infrared5/massroute-pi/Art/Models/Textures/Picture_Texture.png

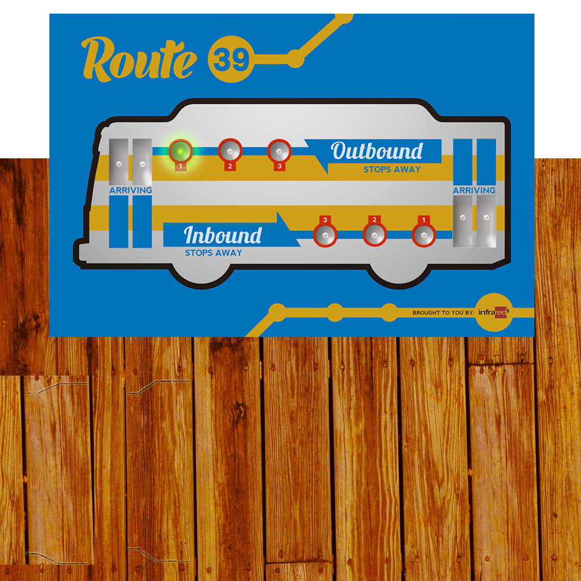
Art/Models/Textures/Picture_Texture.png
