infrared5/massroute-pi/Art/Models/Textures/PictureUV.png

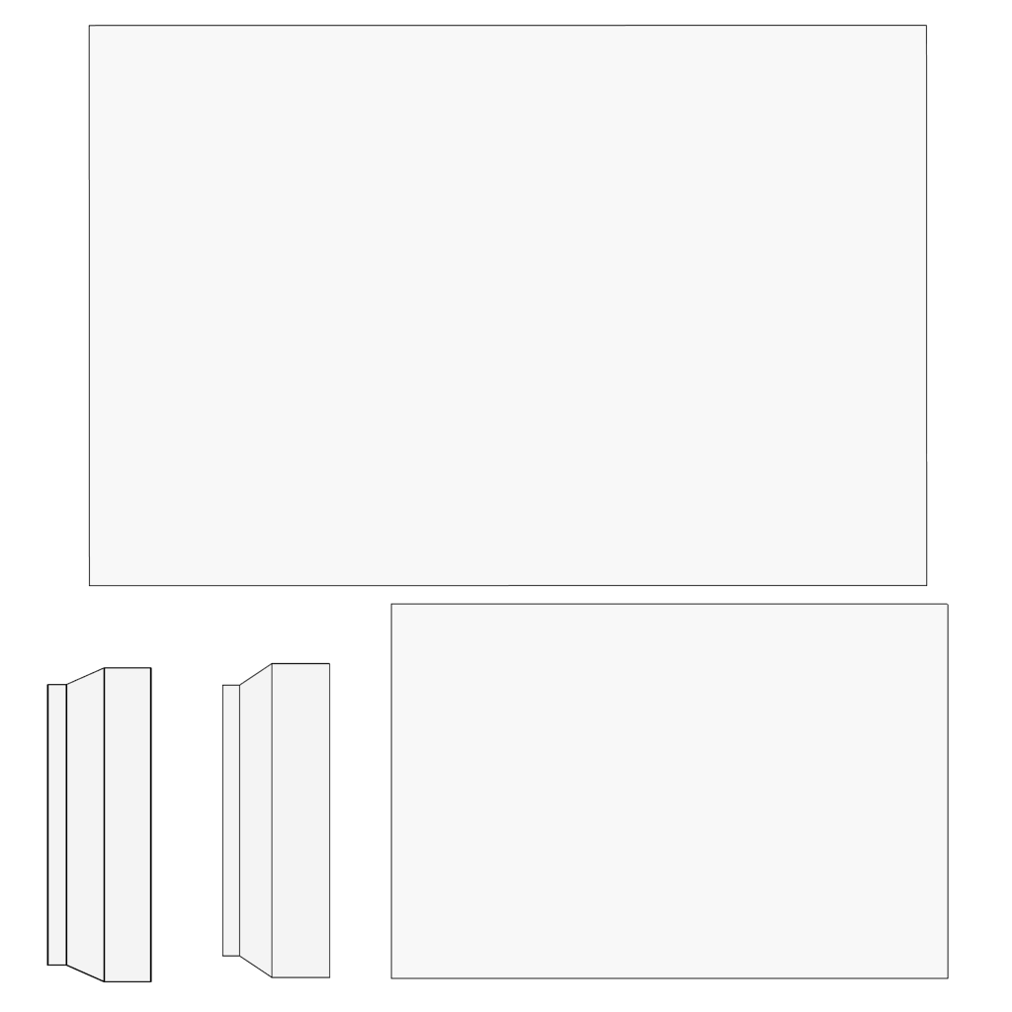
Art/Models/Textures/PictureUV.png
