infrared5/massroute-pi/Art/Research/Americana/4-500x344.jpg

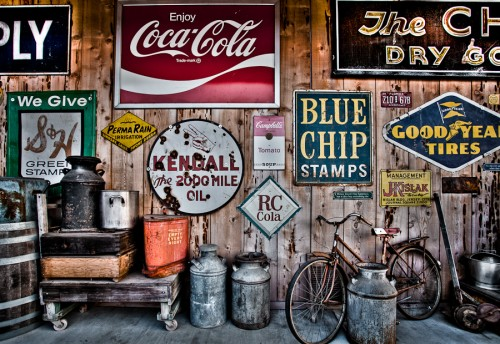
Art/Research/Americana/4-500x344.jpg
