infrared5/massroute-pi/Art/Research/Americana/2363436134_2fb481de5b.jpg

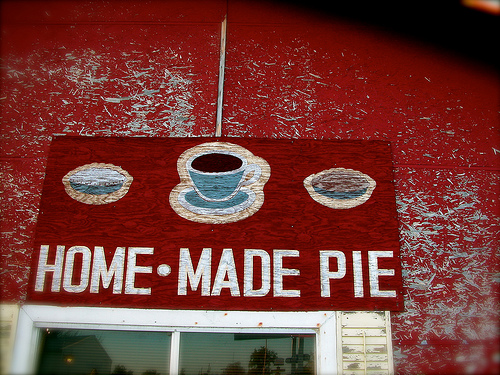
Art/Research/Americana/2363436134_2fb481de5b.jpg
