infrared5/massroute-pi/Art/Research/Americana/200773309354_1_0_1.jpg

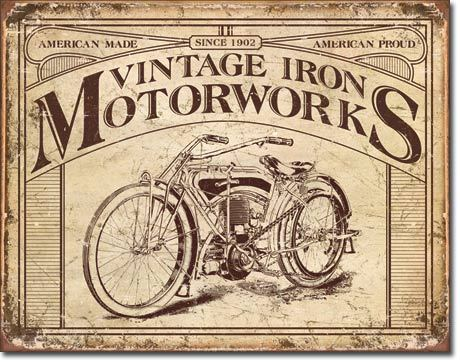
Art/Research/Americana/200773309354_1_0_1.jpg
