infrared5/massroute-pi/Art/Research/Americana/$(KGrHqZHJBME63Uw4Y8SBO76!MFf,g~~60_35.JPG

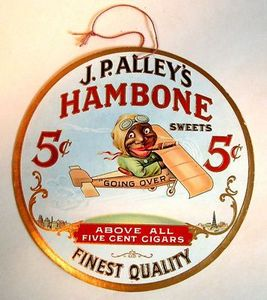
Art/Research/Americana/$(KGrHqZHJBME63Uw4Y8SBO76!MFf,g~~60_35.JPG
