infrared5/massroute-pi/Art/Research/Americana/dont-be-a-drip.jpg

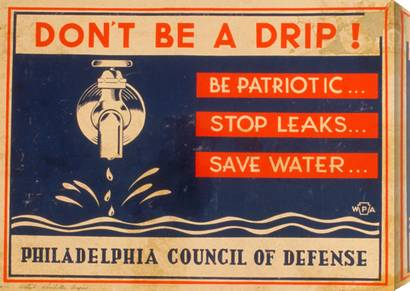
Art/Research/Americana/dont-be-a-drip.jpg
