infrared5/massroute-pi/Art/Research/Americana/il_fullxfull.299568161.jpg

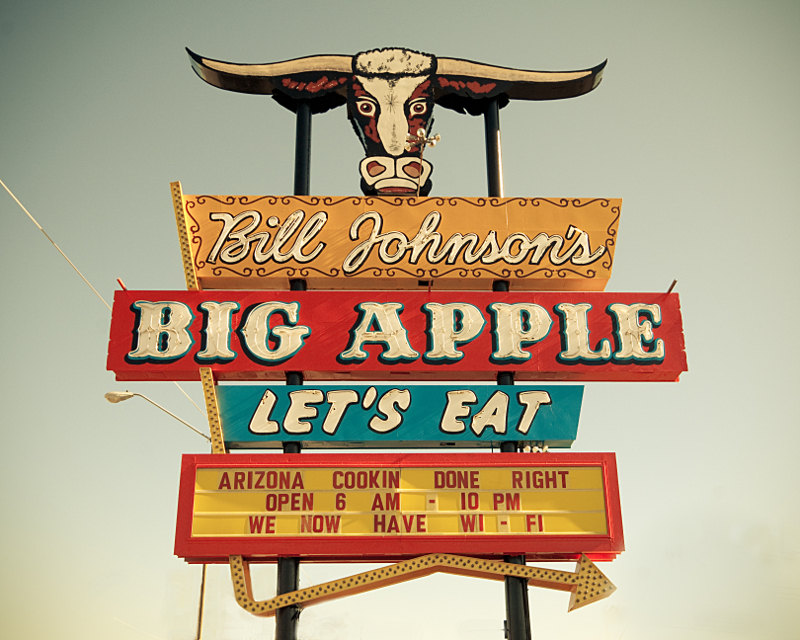
Art/Research/Americana/il_fullxfull.299568161.jpg
