infrared5/massroute-pi/Art/Research/Americana/mX-IDmk9UM7dmhiOSRjjnaw.jpg

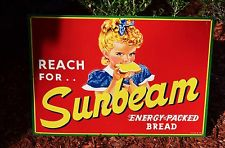
Art/Research/Americana/mX-IDmk9UM7dmhiOSRjjnaw.jpg
