infrared5/massroute-pi/Art/Research/Americana/redhorsesigns_se.jpg

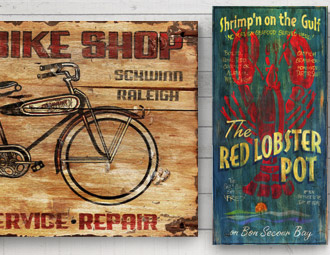
Art/Research/Americana/redhorsesigns_se.jpg
