infrared5/massroute-pi/Art/Research/Americana/set_of_2_vintage_look_advertising_wooden_signs.jpg

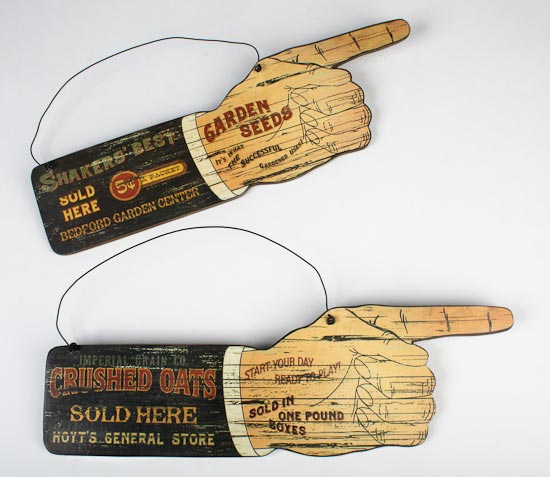
Art/Research/Americana/set_of_2_vintage_look_advertising_wooden_signs.jpg
