infrared5/massroute-pi/Art/Research/Americana/SummerTyne-copy.jpg

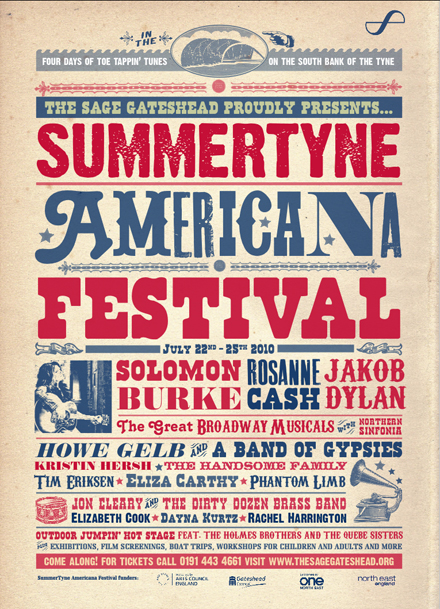
Art/Research/Americana/SummerTyne-copy.jpg
