infrared5/massroute-pi/Art/Research/Bauhaus/bauhaus4.jpg

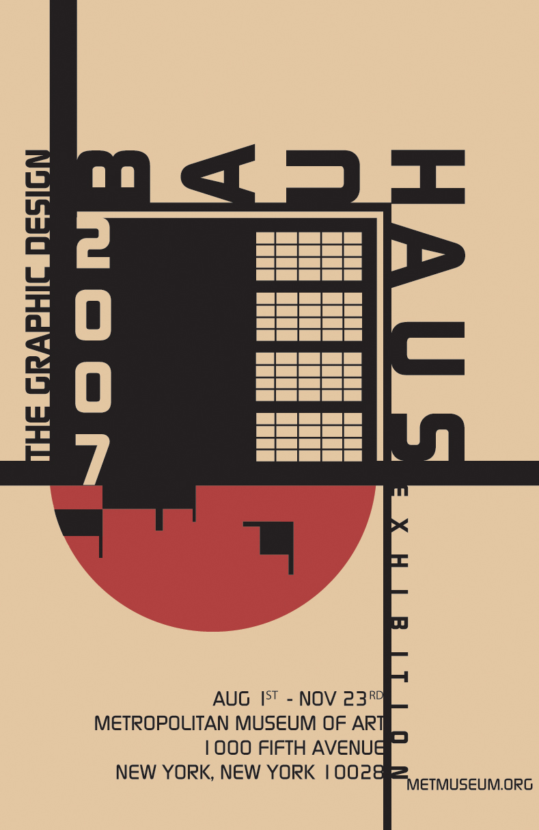
Art/Research/Bauhaus/bauhaus4.jpg
