infrared5/massroute-pi/Art/Research/Bauhaus/bauhaus.jpg

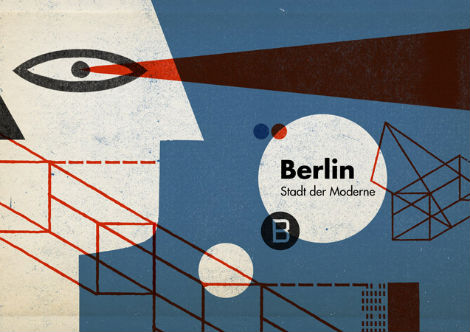
Art/Research/Bauhaus/bauhaus.jpg
