infrared5/massroute-pi/Art/Research/Bauhaus/bauhaus_11.jpg

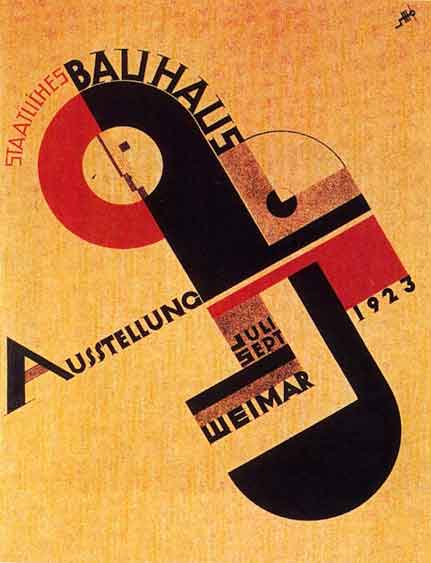
Art/Research/Bauhaus/bauhaus_11.jpg
