infrared5/massroute-pi/Art/Research/Bauhaus/Bauhaus_lecture.jpg

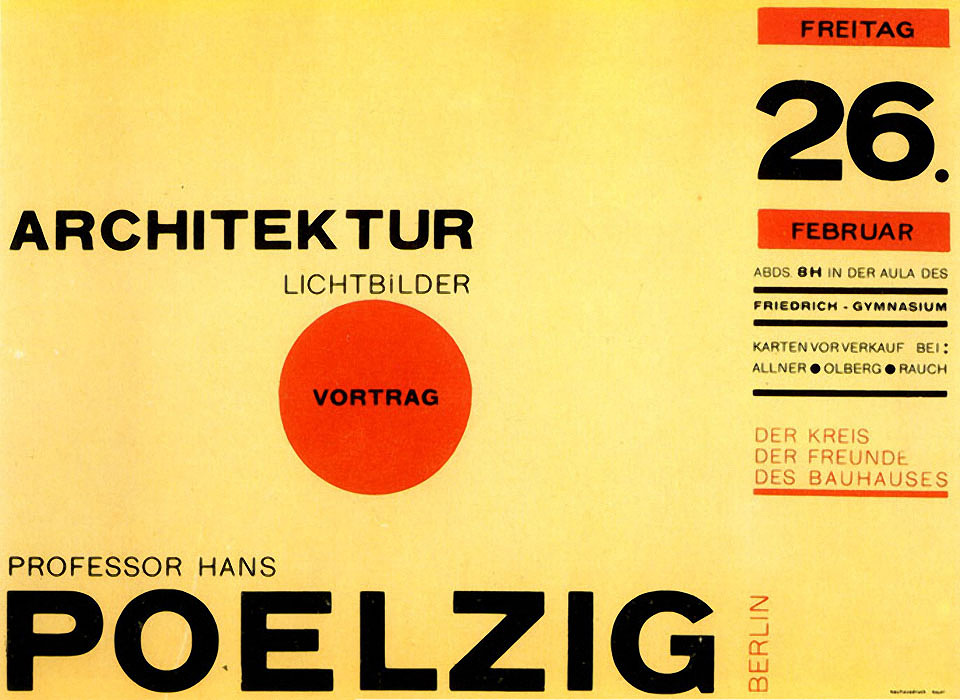
Art/Research/Bauhaus/Bauhaus_lecture.jpg
