infrared5/massroute-pi/Art/Research/Bauhaus/Factory-A-by-Josef-Albers-001.jpg

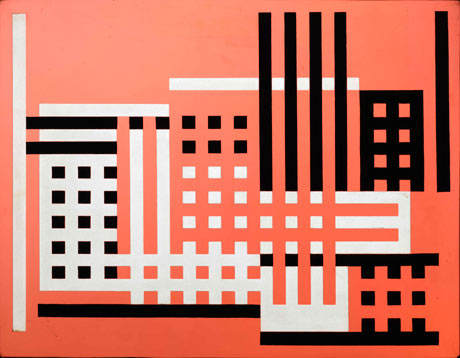
Art/Research/Bauhaus/Factory-A-by-Josef-Albers-001.jpg
