infrared5/massroute-pi/Art/Research/Bauhaus/original_299956_bozZB4MAJBqUJNq1PP5R_KZUT.jpeg

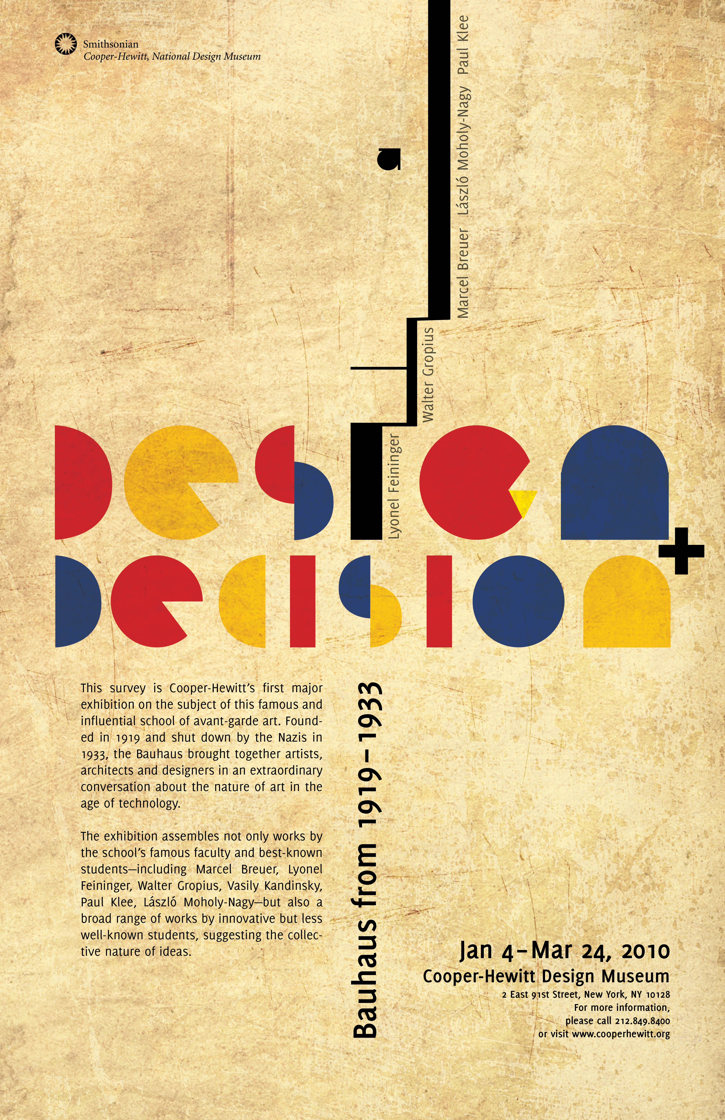
Art/Research/Bauhaus/original_299956_bozZB4MAJBqUJNq1PP5R_KZUT.jpeg
