infrared5/massroute-pi/Art/Research/CityFeed/920x500_city-feed-4_930.jpg

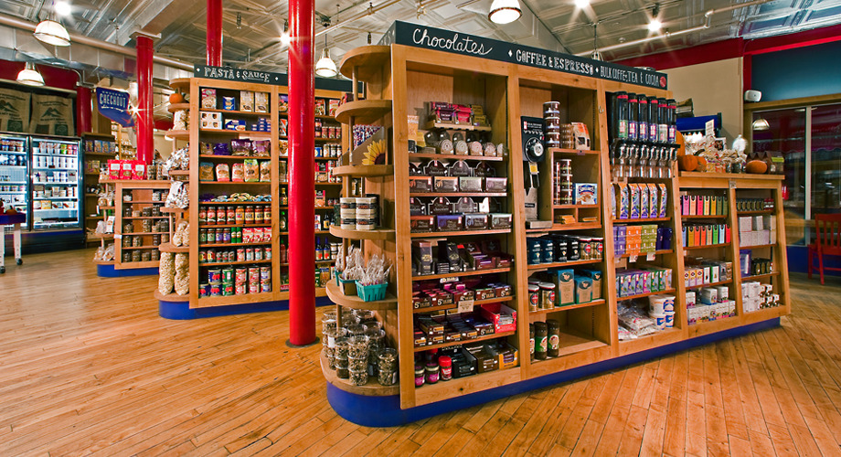
Art/Research/CityFeed/920x500_city-feed-4_930.jpg
