infrared5/massroute-pi/Art/Research/CityFeed/City+Feed-e1346957091311.jpg

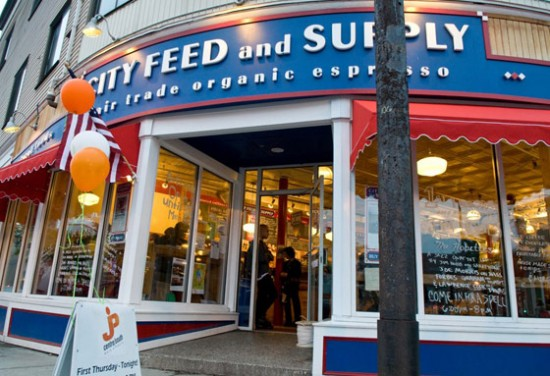
Art/Research/CityFeed/City+Feed-e1346957091311.jpg
