infrared5/massroute-pi/Art/Research/CityFeed/img_2869.jpg

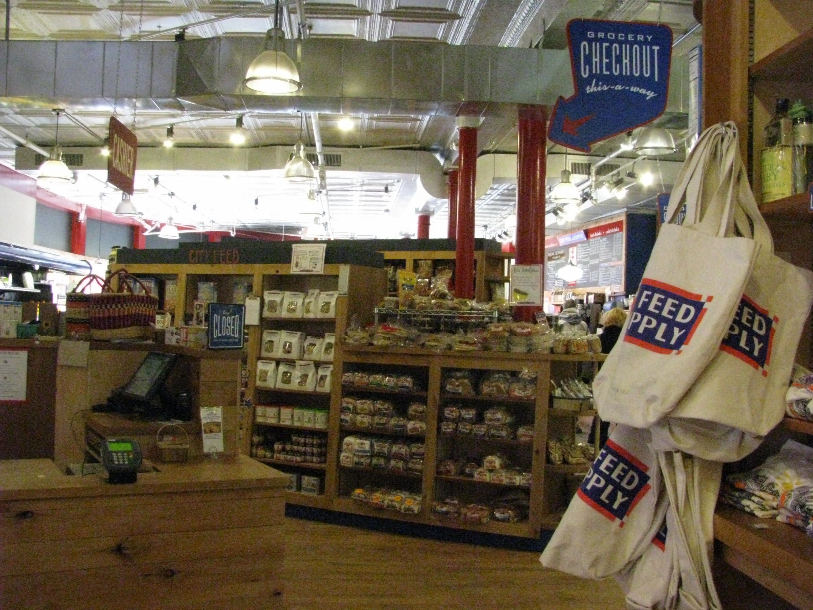
Art/Research/CityFeed/img_2869.jpg
