infrared5/massroute-pi/Art/Research/CityFeed/Interior.jpg

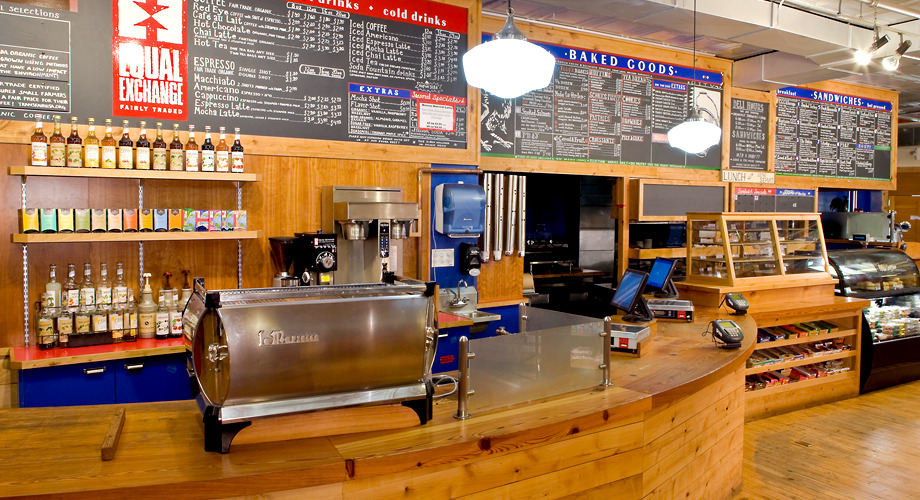
Art/Research/CityFeed/Interior.jpg
