infrared5/massroute-pi/Art/Research/Depression Era/Ar-ykKFCAAA9G-D.jpg

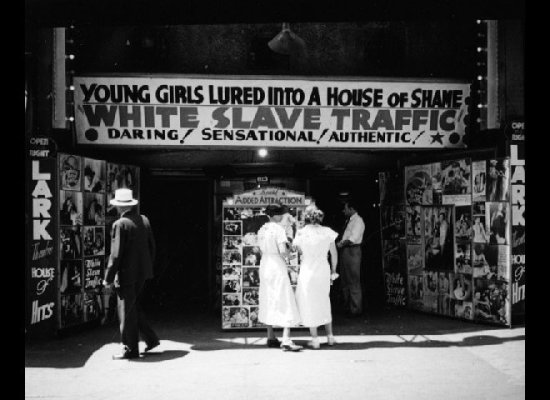
Art/Research/Depression Era/Ar-ykKFCAAA9G-D.jpg
