infrared5/massroute-pi/Art/Research/Futurism/Blog2_Futurism_OtherExamples.jpg

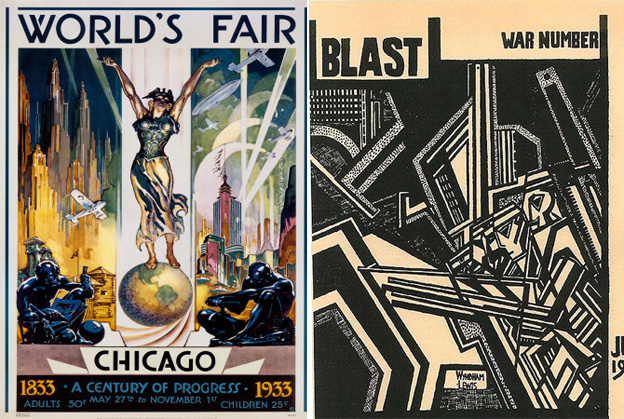
Art/Research/Futurism/Blog2_Futurism_OtherExamples.jpg
