infrared5/massroute-pi/Art/Research/Futurism/fdgall52.jpg

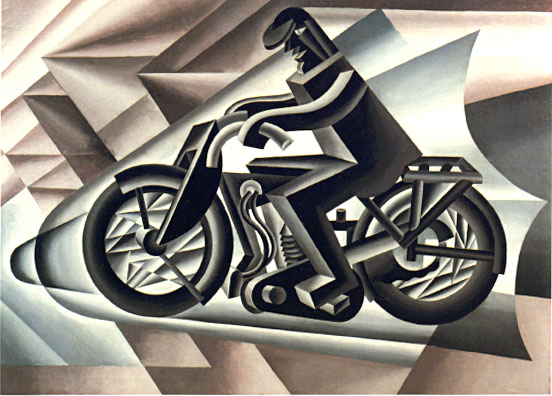
Art/Research/Futurism/fdgall52.jpg
