infrared5/massroute-pi/Art/Research/Futurism/futurism2.jpg

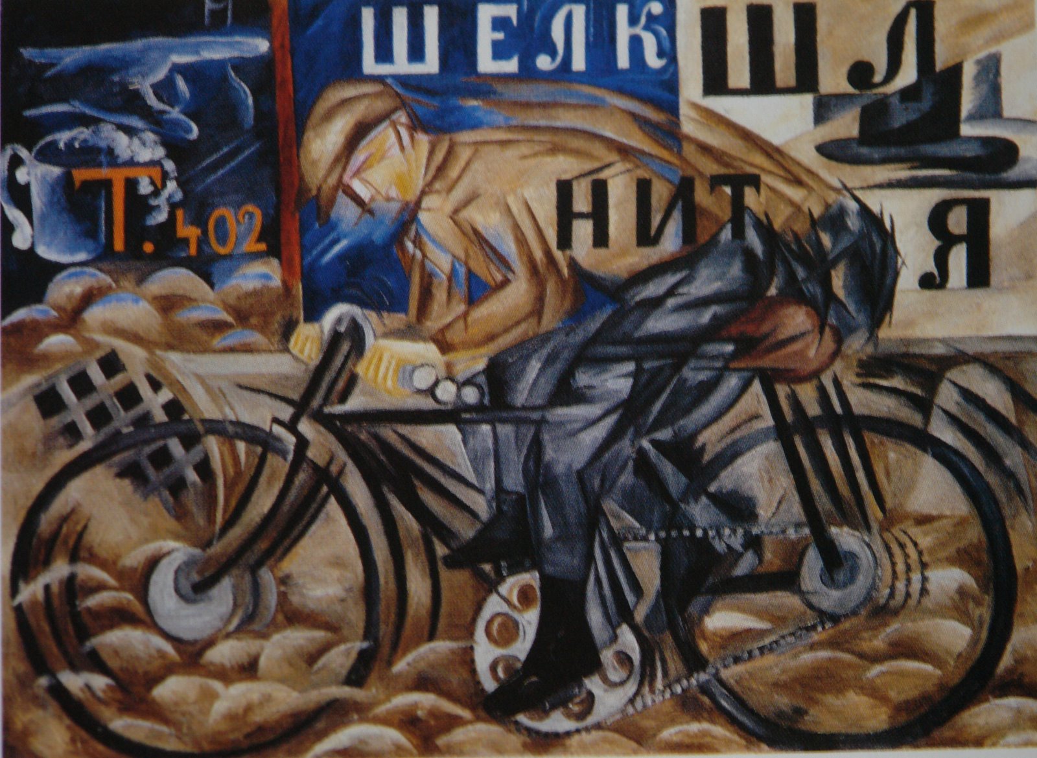
Art/Research/Futurism/futurism2.jpg
