infrared5/massroute-pi/Art/Review/Massroute_WF_02-02.png

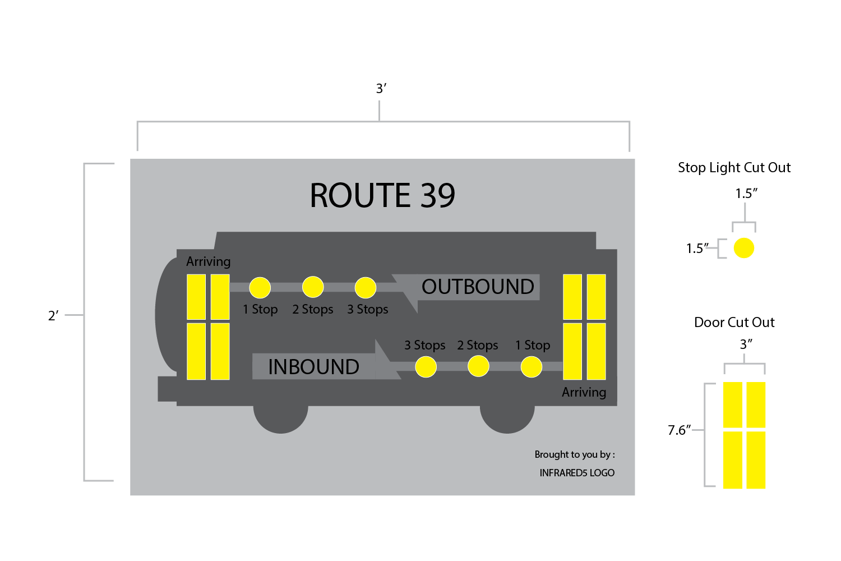
Art/Review/Massroute_WF_02-02.png
