infrared5/massroute-pi/Art/Review/StorePreview.png

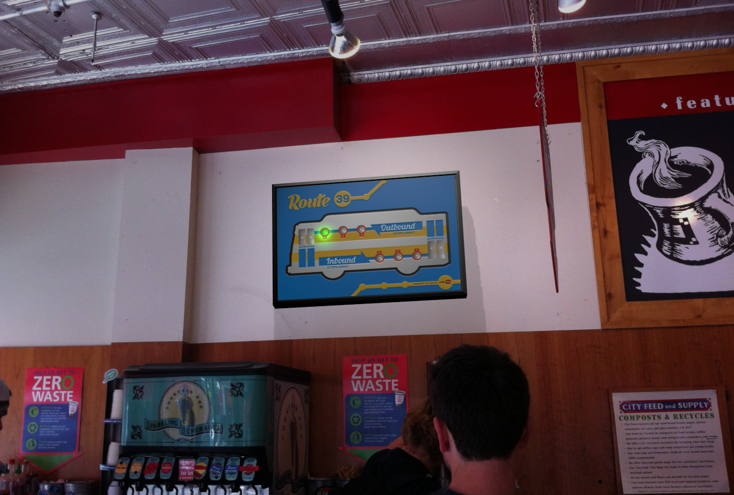
Art/Review/StorePreview.png
