infrared5/massroute-pi/Art/Research/Constructivism/6fa816a37ae9709844cc6d32457d184a.jpg

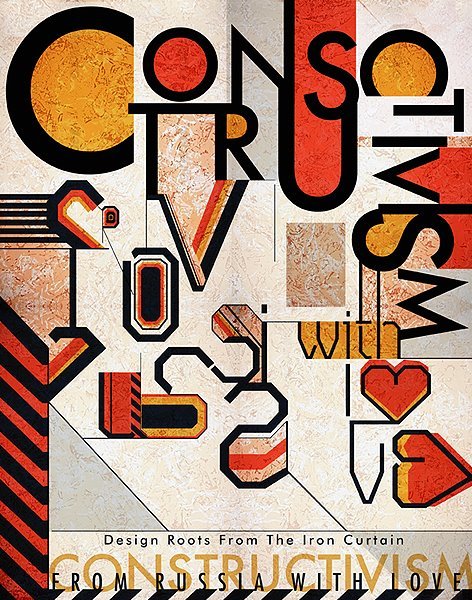
Art/Research/Constructivism/6fa816a37ae9709844cc6d32457d184a.jpg
