infrared5/massroute-pi/Art/Research/Constructivism/840181232772750.jpg

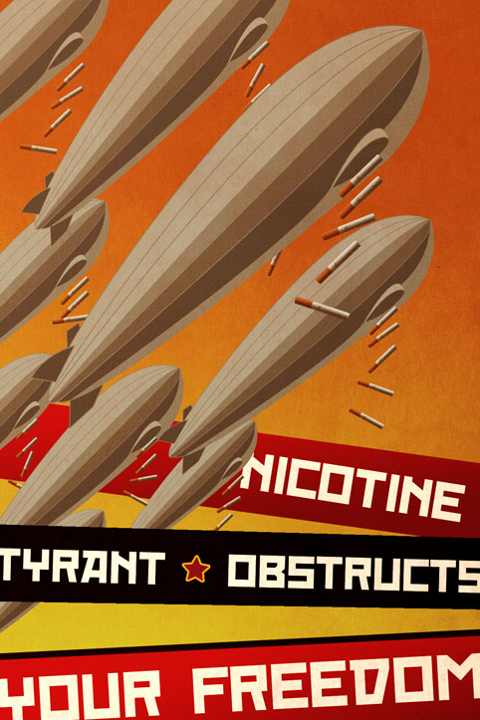
Art/Research/Constructivism/840181232772750.jpg
