infrared5/massroute-pi/Art/Research/Constructivism/GustavKlutsis-Workers-Everyone-must-vote-in-the-Election-of-Soviets-1930.jpg

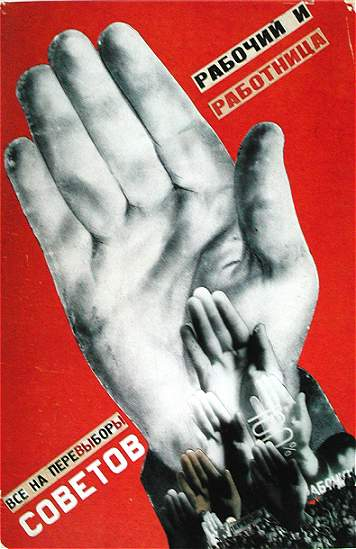
Art/Research/Constructivism/GustavKlutsis-Workers-Everyone-must-vote-in-the-Election-of-Soviets-1930.jpg
