infrared5/massroute-pi/Art/Research/Constructivism/Plakat_mayakowski_gross.jpg

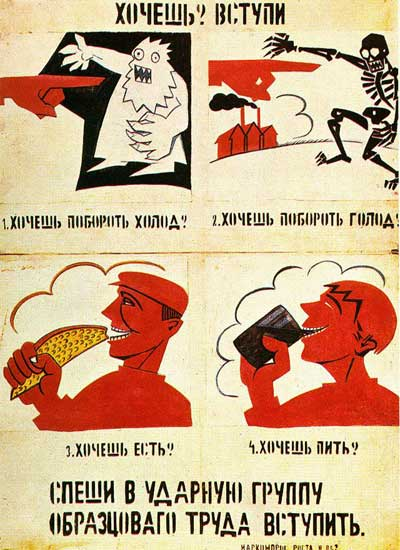
Art/Research/Constructivism/Plakat_mayakowski_gross.jpg
