infrared5/massroute-pi/Art/Research/Constructivism/rodchenko2.jpg

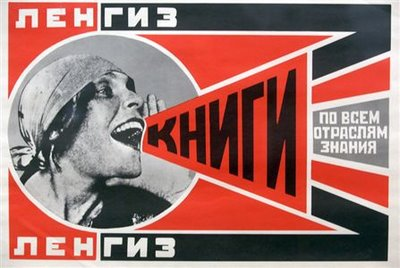
Art/Research/Constructivism/rodchenko2.jpg
