infrared5/massroute-pi/Art/Research/Constructivism/Rodchenko-mayak-nipple.jpg

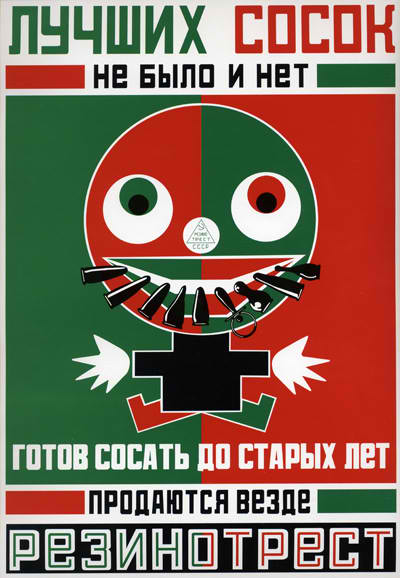
Art/Research/Constructivism/Rodchenko-mayak-nipple.jpg
